FabLabValsamoggia/GustavoTheSpaceman/Mec/Modulo mp3/User Library-MP3-TF-16P.SLDASM

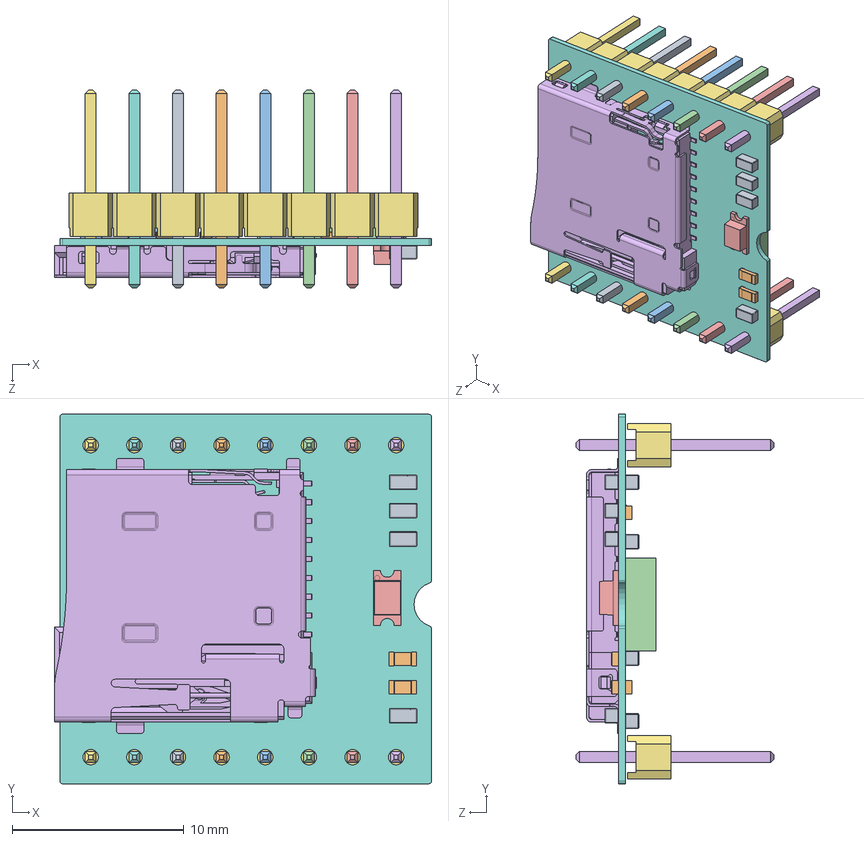
[picture p3: CAD file, 2020-09-24]
Mec/Modulo mp3/User Library-MP3-TF-16P.SLDASM
21.9 x 21.5 x 11.5 mm
User_Library-Chip_Capacitor2CAPC0603X33N x 13
User_Library-res0603-1 x 12
Extruded
Extruded_2
User_Library-FYLS-1206
User_Library-MEM2055-00-190-01-A_revG
Board
