FabLabValsamoggia/GustavoTheSpaceman/Mec/Componenti vari/capc/CAPC0603 v1.step

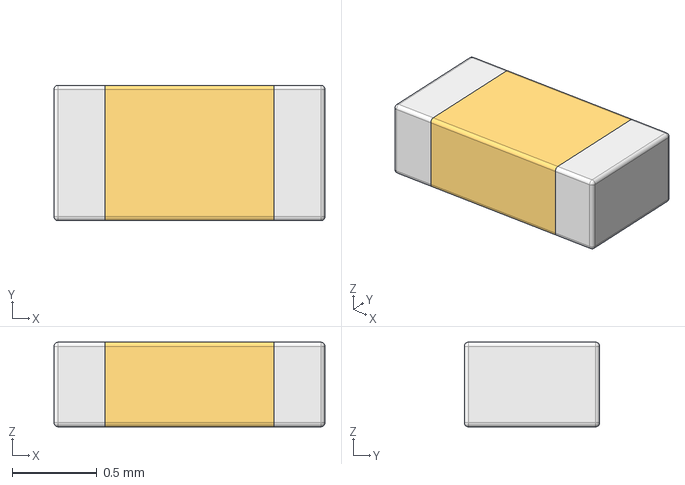
[picture p4: CAD file, 2020-09-24]
Mec/Componenti vari/capc/CAPC0603 v1.step
1.60 x 0.8 x 0.5 mm
