FabLabValsamoggia/GustavoTheSpaceman/Mec/Componenti vari/Push Button SMD/PZ_PushButton.stp

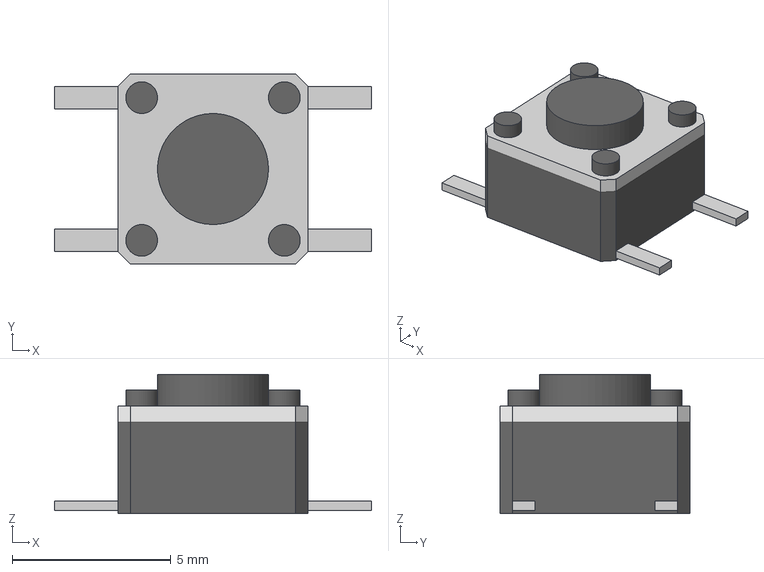
[picture p5: CAD file, 2020-09-24]
Mec/Componenti vari/Push Button SMD/PZ_PushButton.stp
10.0 x 6.00 x 4.40 mm
