FabLabValsamoggia/GustavoTheSpaceman/Mec/Componenti vari/strip/1x3 p2_54mm male.step

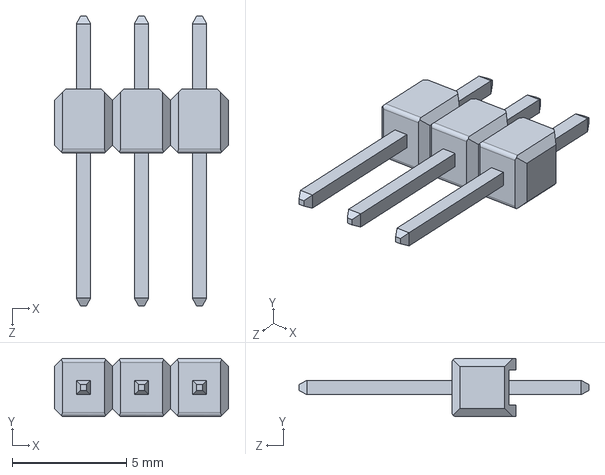
[picture p6: CAD file, 2020-09-24]
Mec/Componenti vari/strip/1x3 p2_54mm male.step
7.62 x 2.54 x 12.7 mm
