FabLabValsamoggia/GustavoTheSpaceman/Mec/Componenti vari/WS2812b/WS2812_RGB_LED_updated.stp

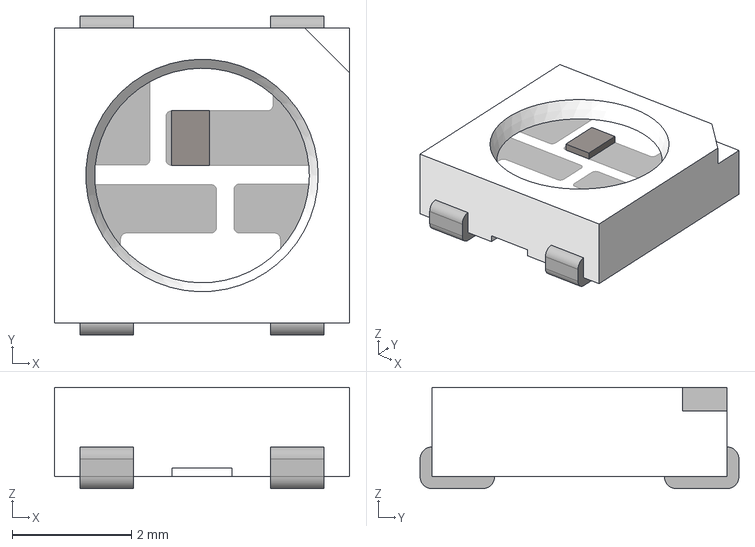
[picture p7: CAD file, 2020-09-24]
Mec/Componenti vari/WS2812b/WS2812_RGB_LED_updated.stp
4.95 x 5.35 x 1.70 mm
