FabLabValsamoggia/GustavoTheSpaceman/Mec/Gustavo/coperchio_rpv03.stl

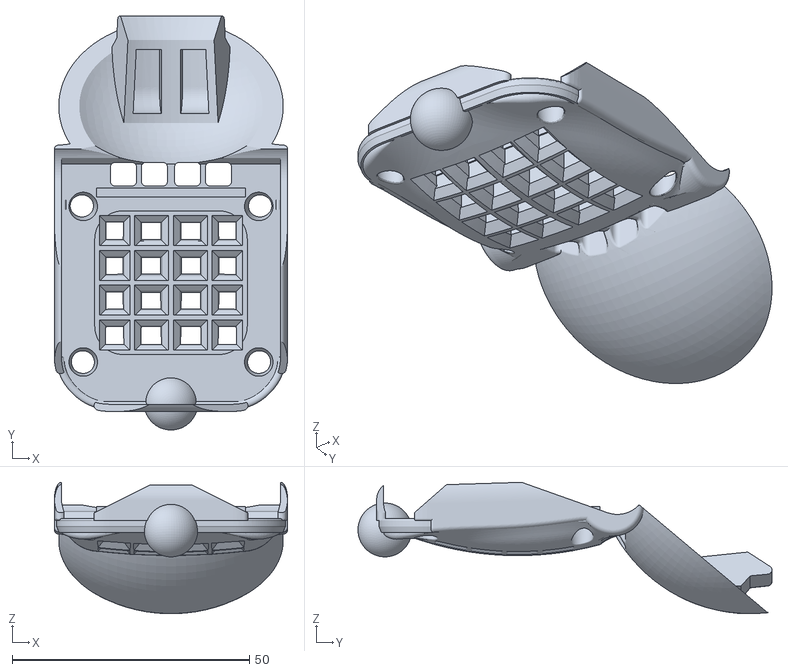
[picture p8: CAD file, 2020-09-24]
Mec/Gustavo/coperchio_rpv03.stl
49.2 x 87.3 x 27.7
