FabLabValsamoggia/GustavoTheSpaceman/Mec/Arduino Nano/Solidworks/User Library-Arduino Nano 3.0_User Library-SW3dPS-atmega8 (tqfp32)_V2008_.SLDPRT

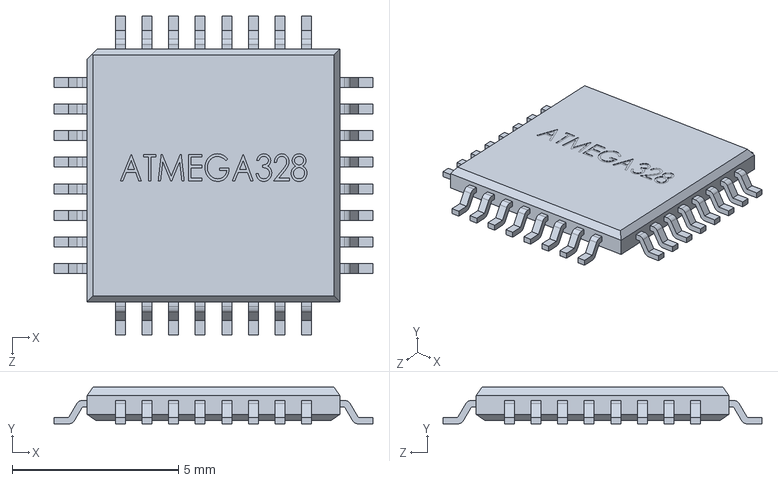
[picture p9: CAD file, 2020-09-24]
Mec/Arduino Nano/Solidworks/User Library-Arduino Nano 3.0_User Library-SW3dPS-atmega8 (tqfp32)_V2008_.SLDPRT
9.60 x 1.11 x 9.60 mm
