FabLabValsamoggia/GustavoTheSpaceman/Mec/Componenti vari/capc/CAPC1206 v2.step

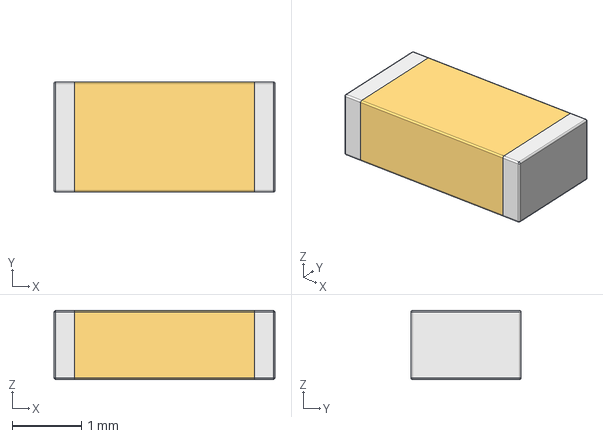
[picture p10: CAD file, 2020-09-24]
Mec/Componenti vari/capc/CAPC1206 v2.step
3.20 x 1.60 x 1.00 mm
