FabLabValsamoggia/GustavoTheSpaceman/Mec/Componenti vari/photoresistor.STEP

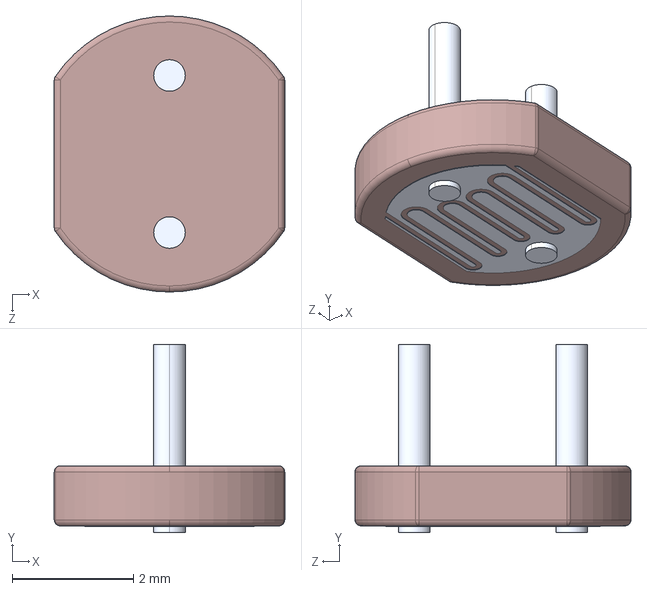
[picture p11: CAD file, 2020-09-24]
Mec/Componenti vari/photoresistor.STEP
3.80 x 3.10 x 4.55 mm
