FabLabValsamoggia/GustavoTheSpaceman/Mec/Componenti vari/strip/SSM-115-L-SV.stp

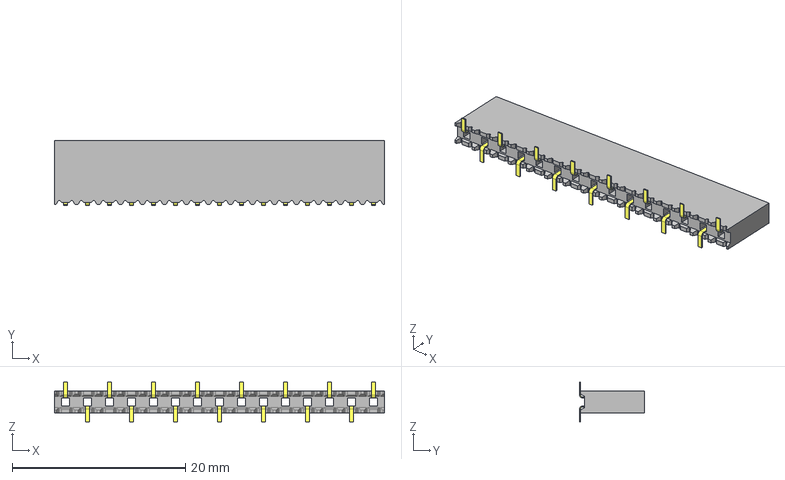
[picture p12: CAD file, 2020-09-24]
Mec/Componenti vari/strip/SSM-115-L-SV.stp
38.1 x 7.49 x 4.57 mm
_SSM-115-L-SV_body
_C-95-0215
