FabLabValsamoggia/GustavoTheSpaceman/Mec/Componenti vari/capc/CAPC0402 v2.step

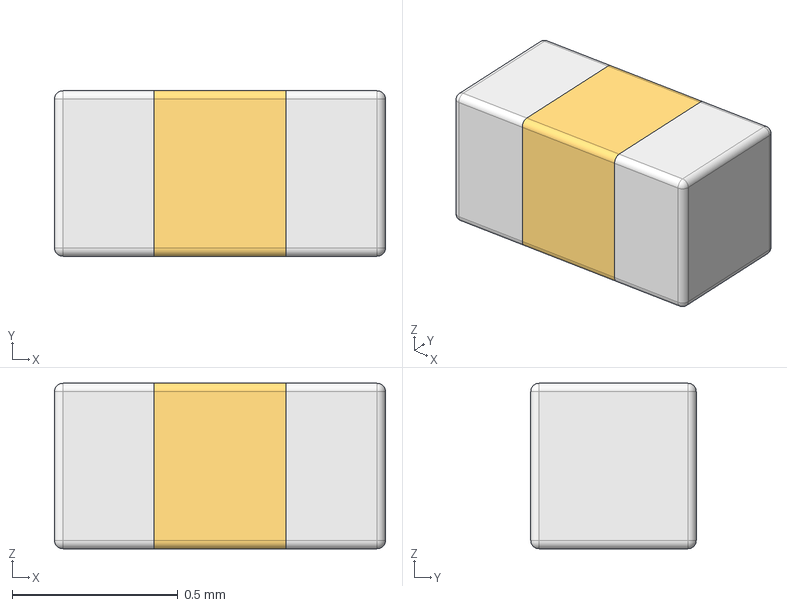
[picture p13: CAD file, 2020-09-24]
Mec/Componenti vari/capc/CAPC0402 v2.step
1.00 x 0.5 x 0.5 mm
