FabLabValsamoggia/GustavoTheSpaceman/Mec/Componenti vari/DO-214AA(SMB).STEP

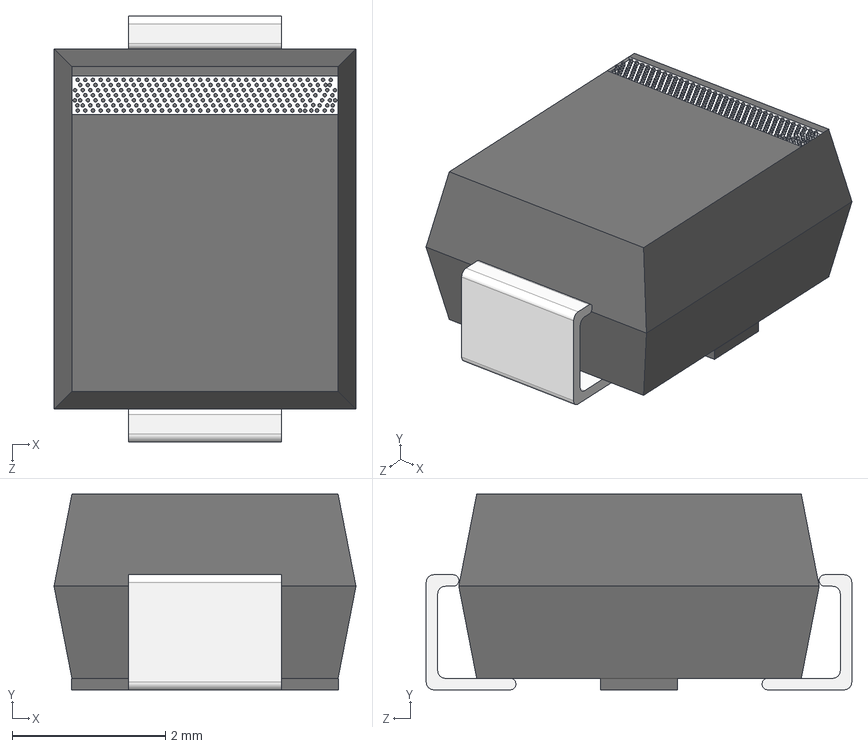
[picture p14: CAD file, 2020-09-24]
Mec/Componenti vari/DO-214AA(SMB).STEP
3.94 x 2.55 x 5.55 mm
