FabLabValsamoggia/GustavoTheSpaceman/Mec/Componenti vari/strip/1x2 p2.54mm male.step

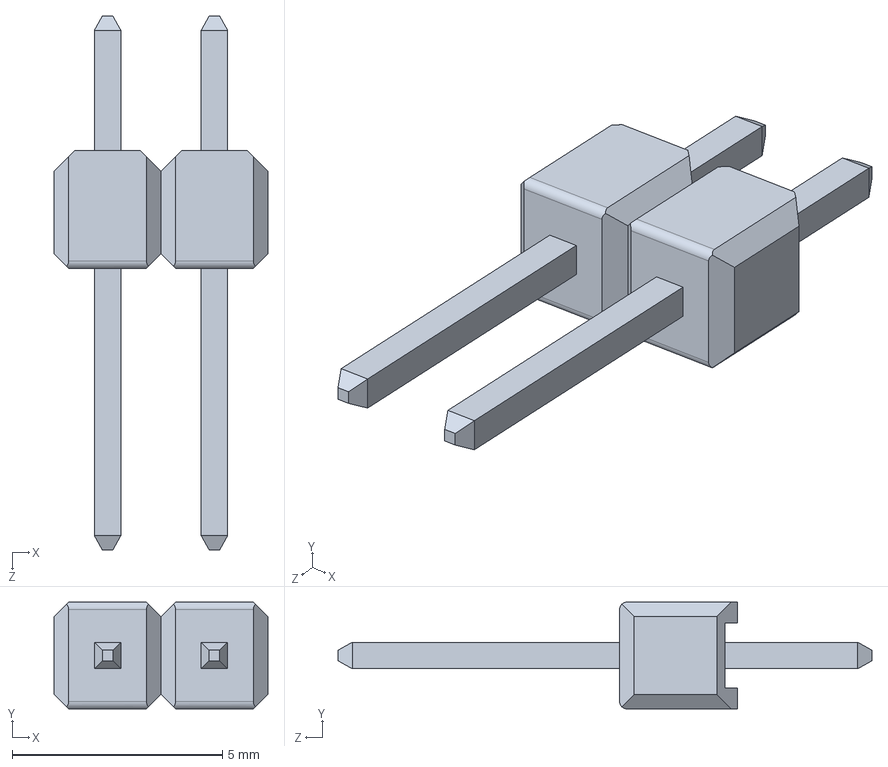
[picture p15: CAD file, 2020-09-24]
Mec/Componenti vari/strip/1x2 p2.54mm male.step
5.08 x 2.54 x 12.7 mm
