FabLabValsamoggia/GustavoTheSpaceman/Mec/Componenti vari/0805_RES.stp

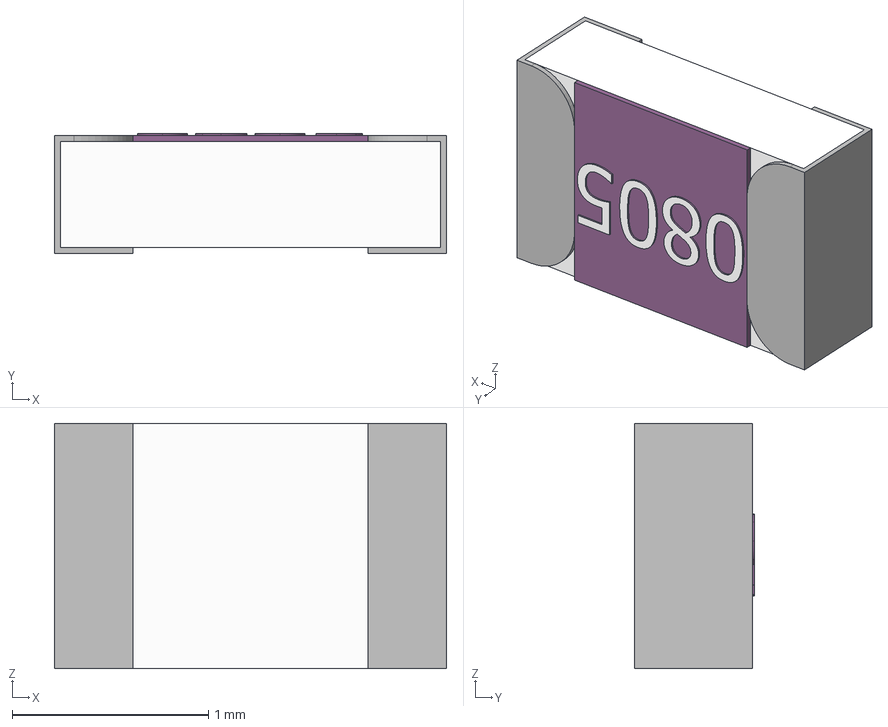
[picture p16: CAD file, 2020-09-24]
Mec/Componenti vari/0805_RES.stp
2.00 x 0.61 x 1.25 mm
Encapsulation x 2
capsule
TopCover
