FabLabValsamoggia/GustavoTheSpaceman/Mec/Componenti vari/capc/CAPC0805 v2.step

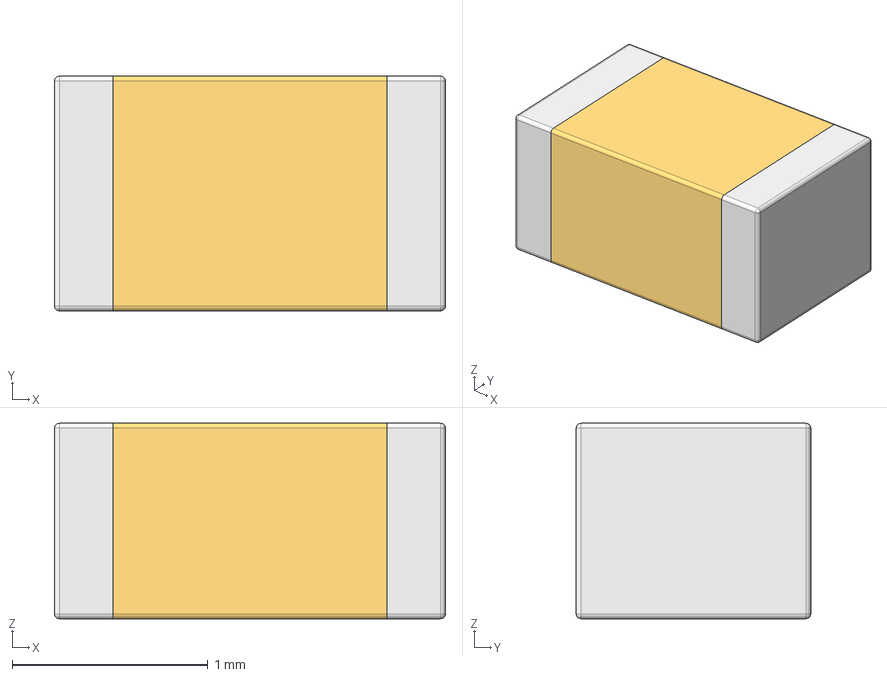
[picture p17: CAD file, 2020-09-24]
Mec/Componenti vari/capc/CAPC0805 v2.step
2.00 x 1.20 x 1.00 mm
