FabLabValsamoggia/GustavoTheSpaceman/Mec/Componenti vari/SSM-108-S-SV.stp

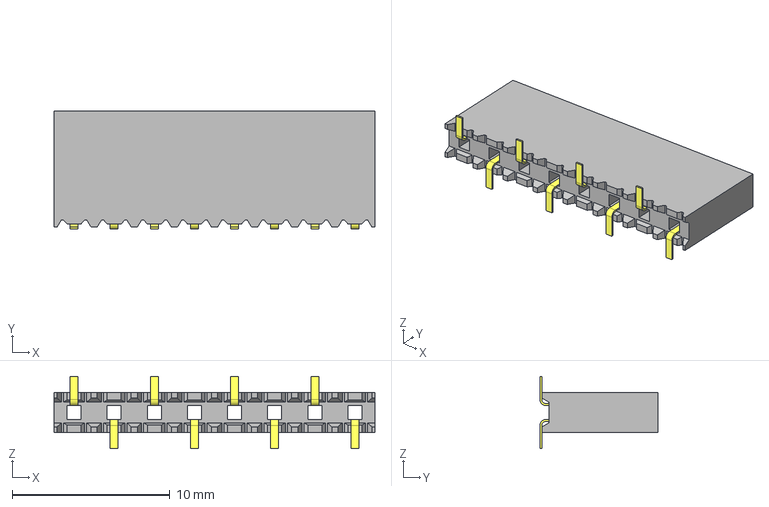
[picture p18: CAD file, 2020-09-24]
Mec/Componenti vari/SSM-108-S-SV.stp
20.3 x 7.49 x 4.57 mm
_SSM-108-S-SV_body
_C-95-028
