FabLabValsamoggia/GustavoTheSpaceman/Mec/Componenti vari/Diode SMA.stp

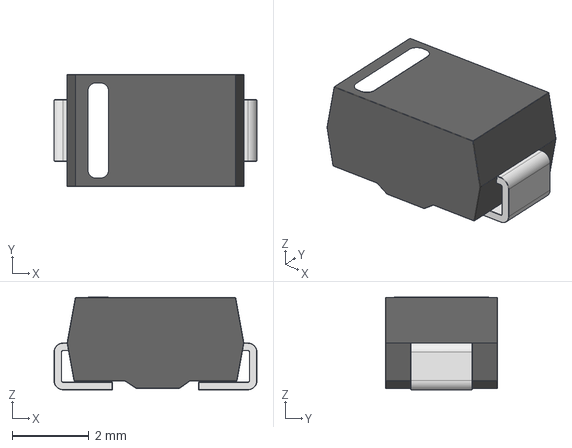
[picture p19: CAD file, 2020-09-24]
Mec/Componenti vari/Diode SMA.stp
5.28 x 2.92 x 2.41 mm
