FabLabValsamoggia/GustavoTheSpaceman/Mec/Componenti vari/TMX-12H.stp

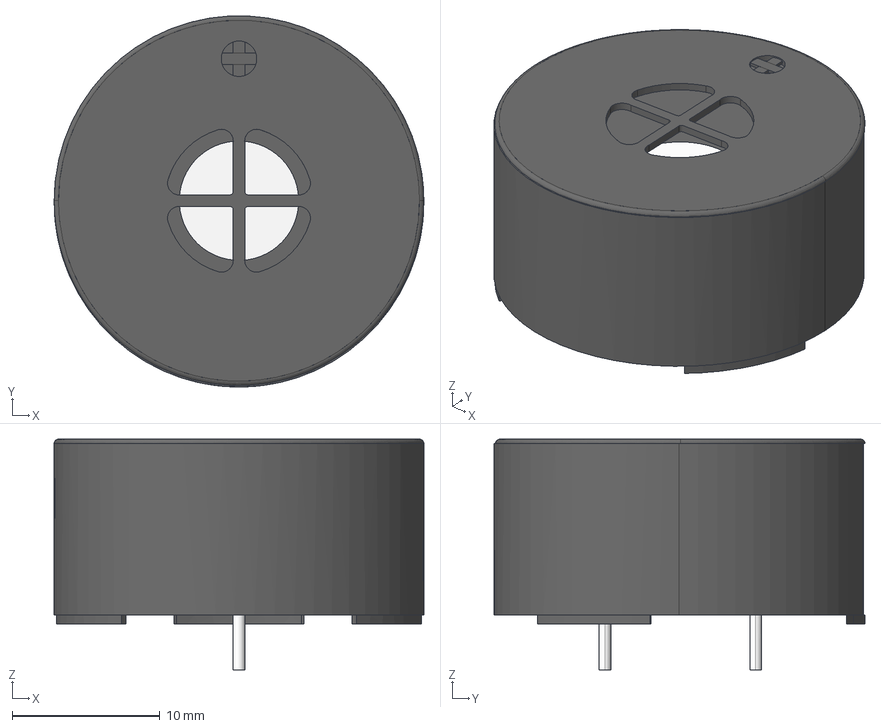
[picture p20: CAD file, 2020-09-24]
Mec/Componenti vari/TMX-12H.stp
25.0 x 25.1 x 15.6 mm
