FabLabValsamoggia/GustavoTheSpaceman/Mec/Arduino Nano/Solidworks/User Library-Arduino Nano 3.0_Arduino Nano 3.0 Bare PCB.SLDPRT

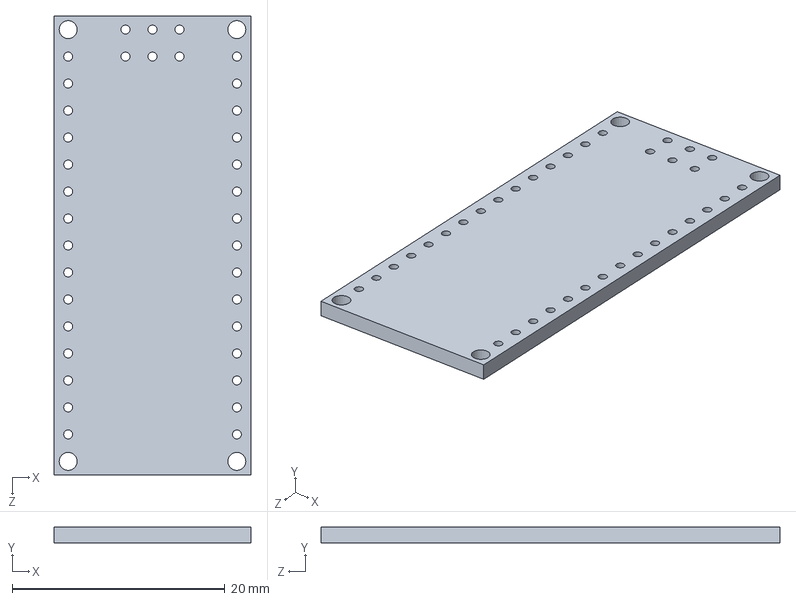
[picture p21: CAD file, 2020-09-24]
Mec/Arduino Nano/Solidworks/User Library-Arduino Nano 3.0_Arduino Nano 3.0 Bare PCB.SLDPRT
18.5 x 1.50 x 43.2 mm
