FabLabValsamoggia/GustavoTheSpaceman/Mec/Componenti vari/sot23 v2.step

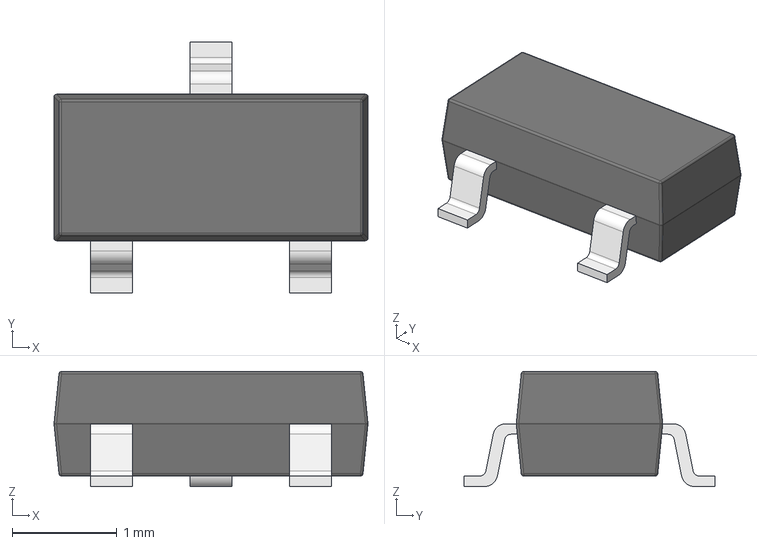
[picture p22: CAD file, 2020-09-24]
Mec/Componenti vari/sot23 v2.step
3.00 x 2.40 x 1.10 mm
pin x 3
