FabLabValsamoggia/GustavoTheSpaceman/Mec/Componenti vari/buzzer.stp

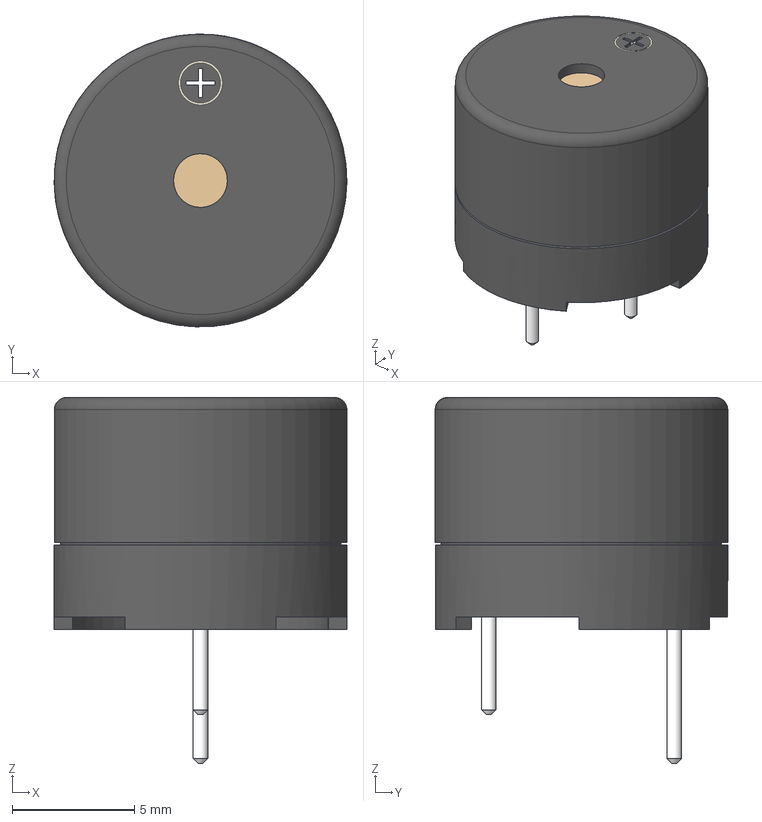
[picture p23: CAD file, 2020-09-24]
Mec/Componenti vari/buzzer.stp
12.0 x 12.0 x 15.0 mm
