FabLabValsamoggia/GustavoTheSpaceman/Mec/Componenti vari/Buzzer TDK.STEP

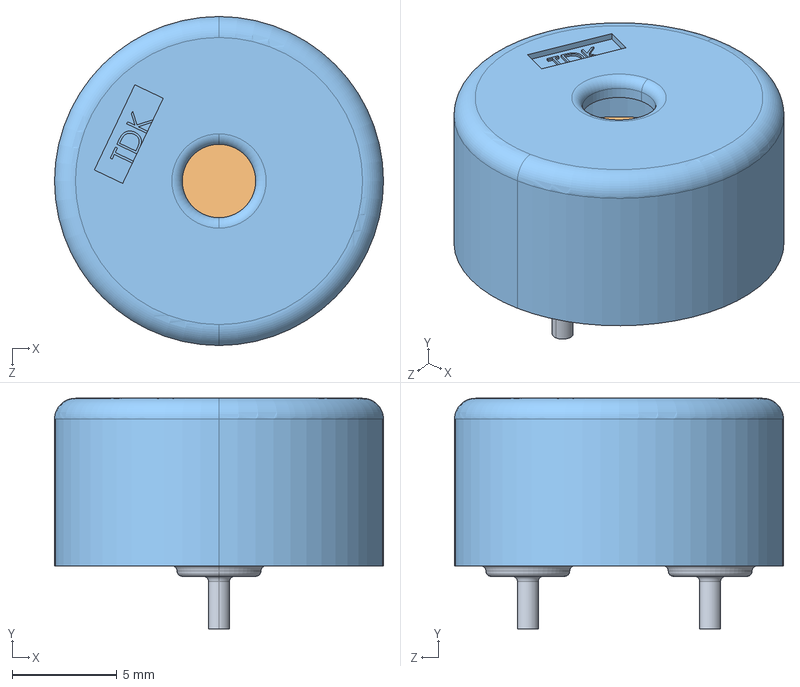
[picture p24: CAD file, 2020-09-24]
Mec/Componenti vari/Buzzer TDK.STEP
15.7 x 11.0 x 15.7 mm
