FabLabValsamoggia/GustavoTheSpaceman/Mec/Arduino Nano/Solidworks/User Library-Arduino Nano 3.0_Capacitor 0805.SLDPRT

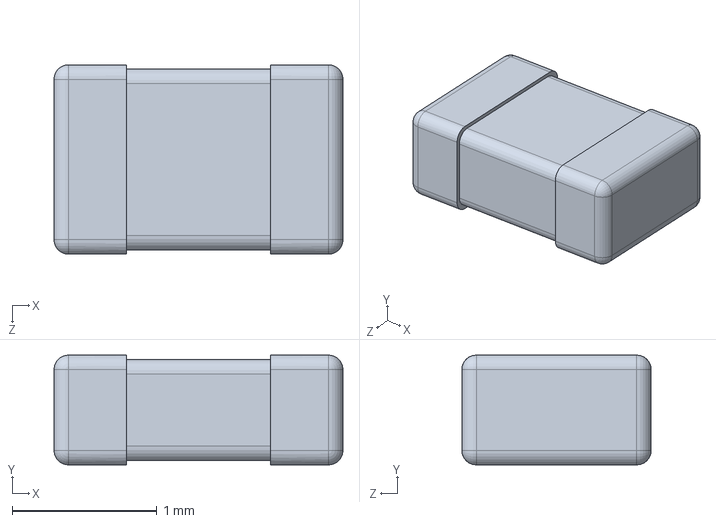
[picture p25: CAD file, 2020-09-24]
Mec/Arduino Nano/Solidworks/User Library-Arduino Nano 3.0_Capacitor 0805.SLDPRT
2.00 x 0.76 x 1.31 mm
