FabLabValsamoggia/GustavoTheSpaceman/Mec/Arduino Nano/Solidworks/User Library-Arduino Nano 3.0_User Library-SSOP-28-FT232RL_.SLDPRT

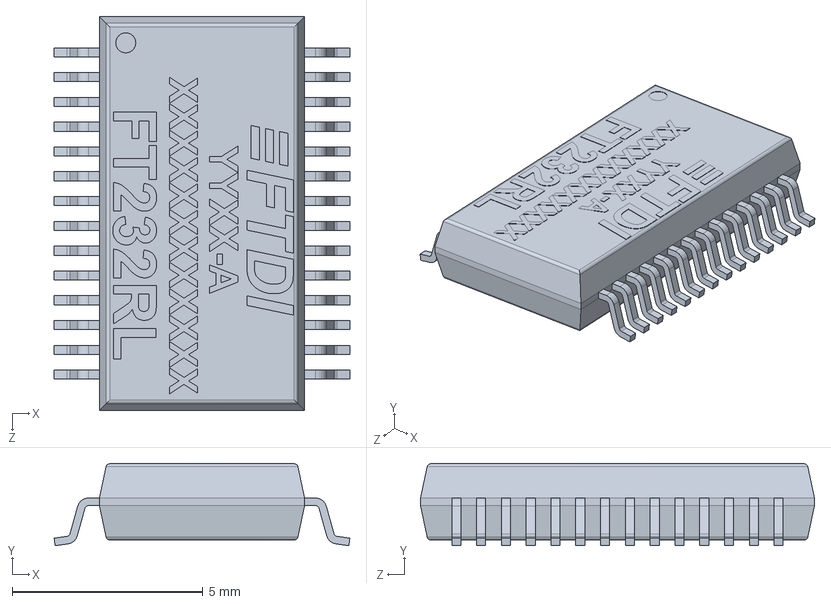
[picture p26: CAD file, 2020-09-24]
Mec/Arduino Nano/Solidworks/User Library-Arduino Nano 3.0_User Library-SSOP-28-FT232RL_.SLDPRT
7.76 x 2.16 x 10.3 mm
