FabLabValsamoggia/GustavoTheSpaceman/Mec/Arduino Nano/Solidworks/User Library-Arduino Nano 3.0_LED 1206 Blue.SLDPRT

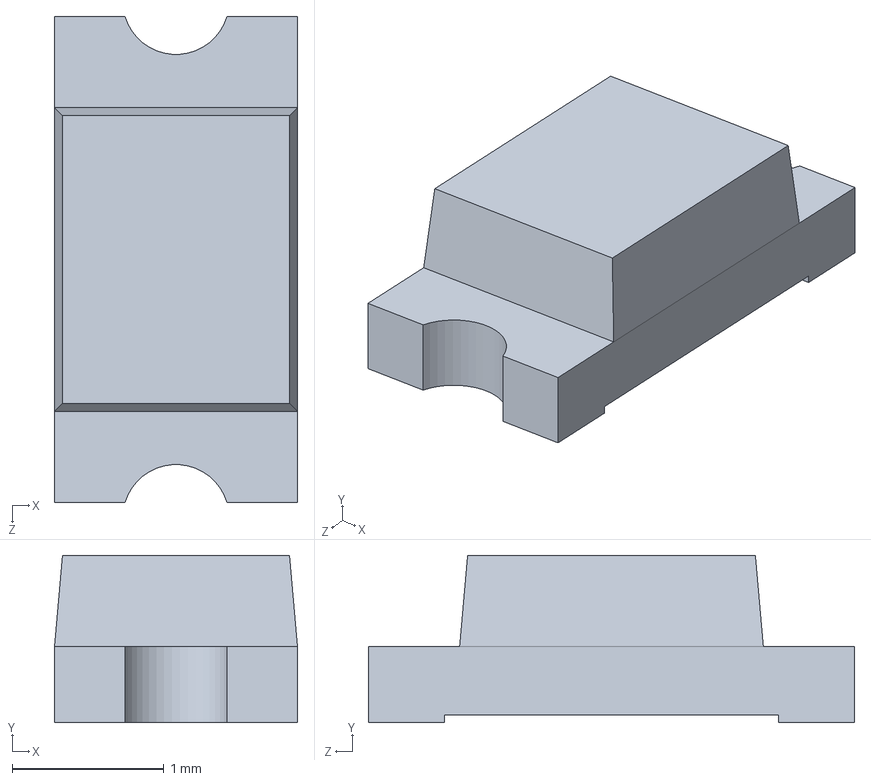
[picture p27: CAD file, 2020-09-24]
Mec/Arduino Nano/Solidworks/User Library-Arduino Nano 3.0_LED 1206 Blue.SLDPRT
1.60 x 1.10 x 3.20 mm
