FabLabValsamoggia/GustavoTheSpaceman/Mec/Arduino Nano/Solidworks/User Library-Arduino Nano 3.0_HDR2x3.SLDPRT

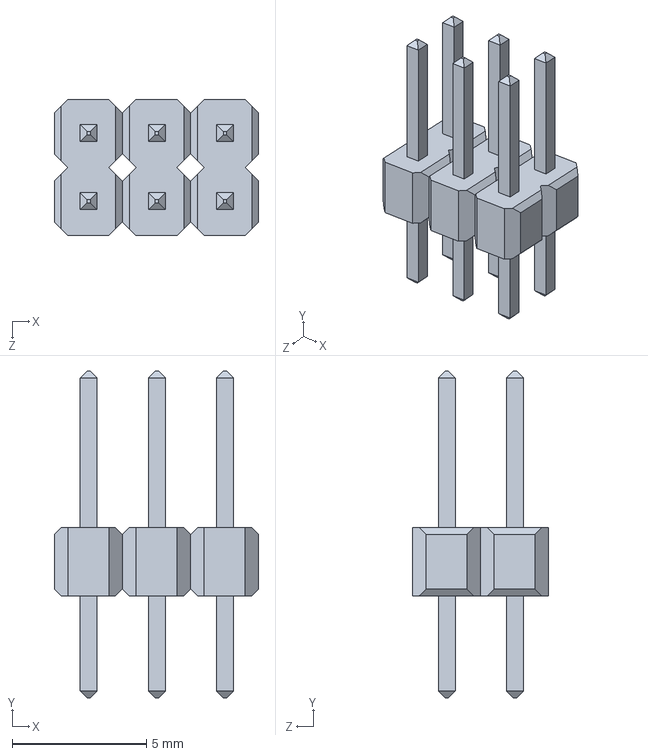
[picture p28: CAD file, 2020-09-24]
Mec/Arduino Nano/Solidworks/User Library-Arduino Nano 3.0_HDR2x3.SLDPRT
7.62 x 12.2 x 5.08 mm
