FabLabValsamoggia/GustavoTheSpaceman/Mec/Arduino Nano/Solidworks/User Library-Arduino Nano 3.0_SOT-223.SLDPRT

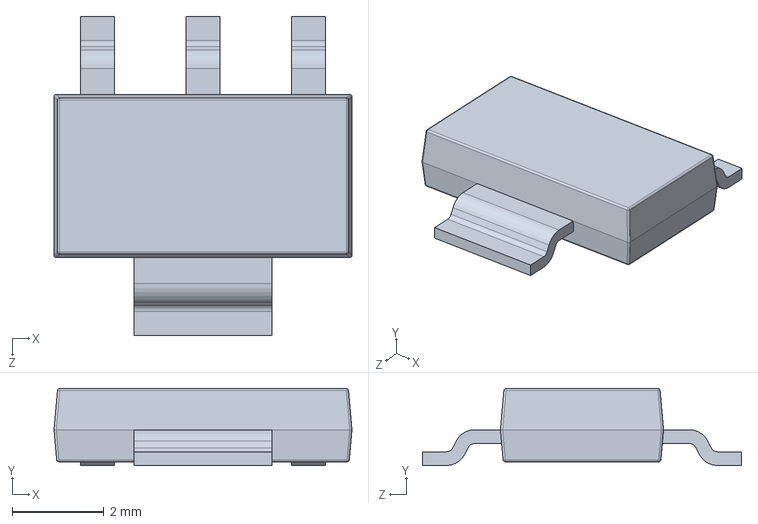
[picture p29: CAD file, 2020-09-24]
Mec/Arduino Nano/Solidworks/User Library-Arduino Nano 3.0_SOT-223.SLDPRT
6.50 x 1.68 x 6.96 mm
