FabLabValsamoggia/GustavoTheSpaceman/Mec/Arduino Nano/Solidworks/User Library-Arduino Nano 3.0_HDR1x15.SLDPRT

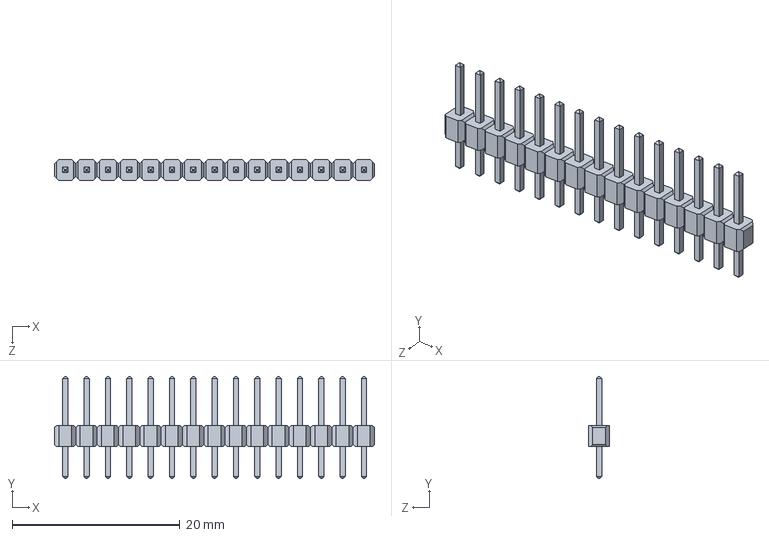
[picture p30: CAD file, 2020-09-24]
Mec/Arduino Nano/Solidworks/User Library-Arduino Nano 3.0_HDR1x15.SLDPRT
38.1 x 12.2 x 2.54 mm
