FabLabValsamoggia/GustavoTheSpaceman/Mec/Arduino Nano/Solidworks/User Library-Arduino Nano 3.0_User Library-Tantalum Capacitor Case R_Tantalum case R part1.SLDPRT

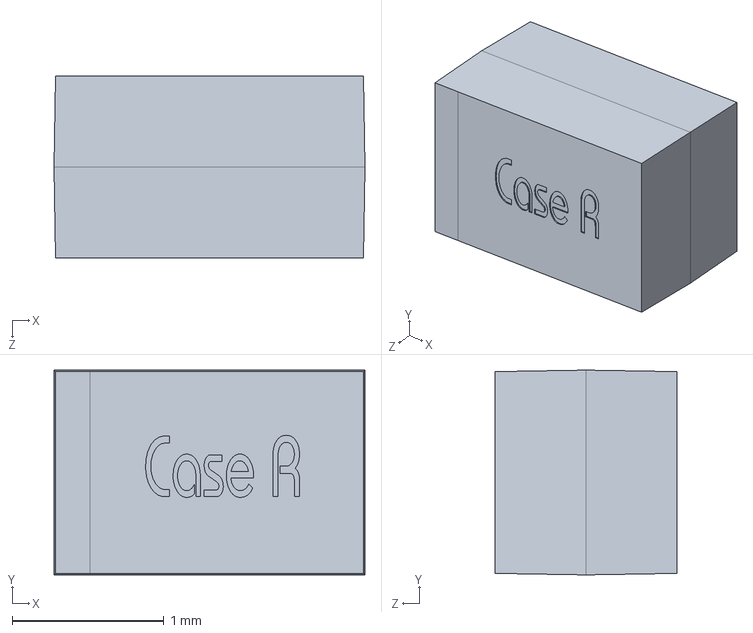
[picture p31: CAD file, 2020-09-24]
Mec/Arduino Nano/Solidworks/User Library-Arduino Nano 3.0_User Library-Tantalum Capacitor Case R_Tantalum case R part1.SLDPRT
2.05 x 1.35 x 1.20 mm
