FabLabValsamoggia/GustavoTheSpaceman/Mec/Arduino Nano/Solidworks/User Library-Arduino Nano 3.0_User Library-Tantalum Capacitor Case R_Tantalum case R part2.SLDPRT

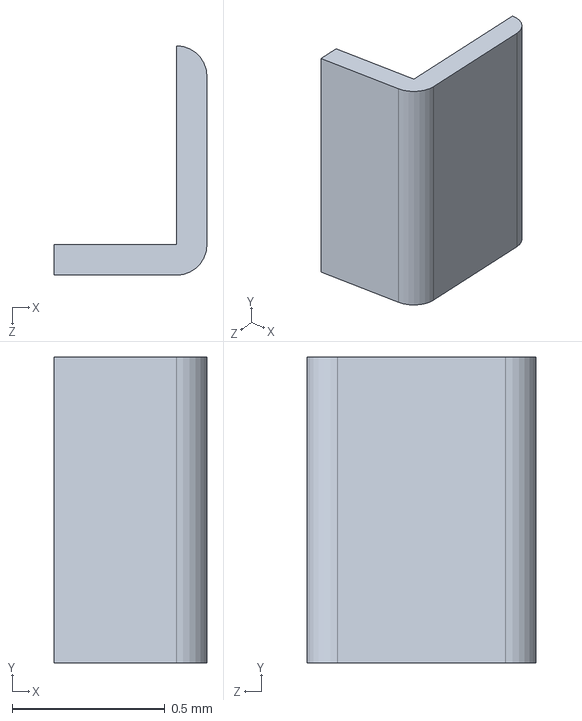
[picture p32: CAD file, 2020-09-24]
Mec/Arduino Nano/Solidworks/User Library-Arduino Nano 3.0_User Library-Tantalum Capacitor Case R_Tantalum case R part2.SLDPRT
0.5 x 1.00 x 0.75 mm
