FabLabValsamoggia/GustavoTheSpaceman/Mec/Arduino Nano/Solidworks/User Library-Arduino Nano 3.0_User Library-548190572_USBBMINI_.SLDPRT

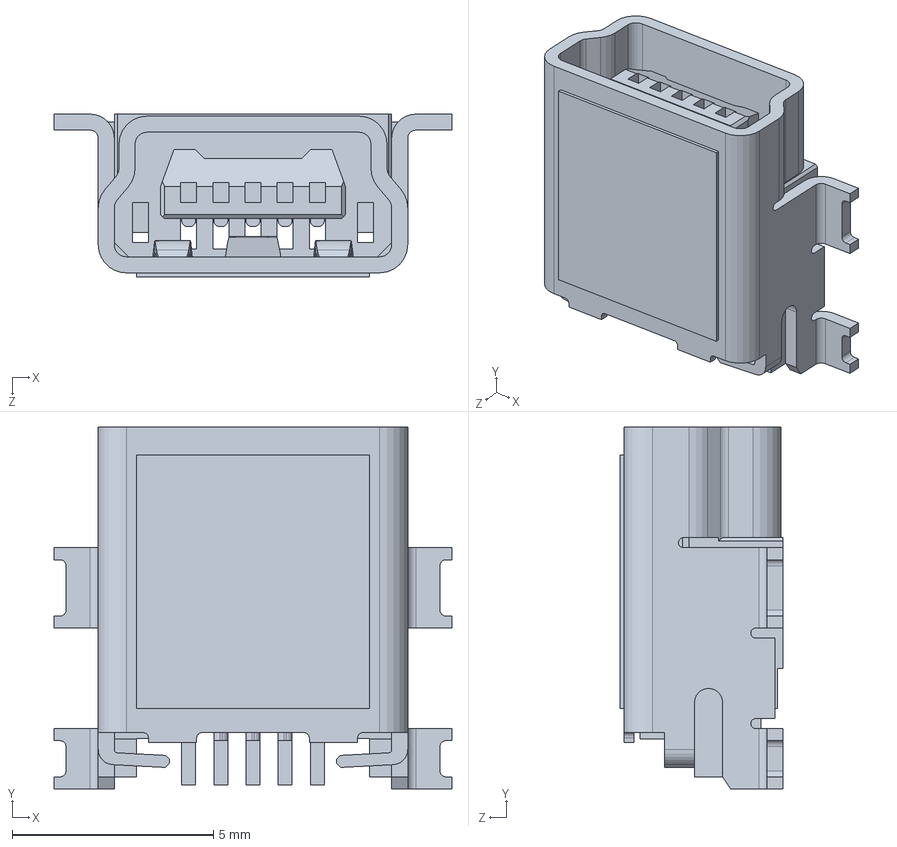
[picture p33: CAD file, 2020-09-24]
Mec/Arduino Nano/Solidworks/User Library-Arduino Nano 3.0_User Library-548190572_USBBMINI_.SLDPRT
9.90 x 9.00 x 4.05 mm
