FabLabValsamoggia/GustavoTheSpaceman/Mec/Arduino Nano/Solidworks/User Library-Arduino Nano 3.0_User Library-TUMD2.sldasm

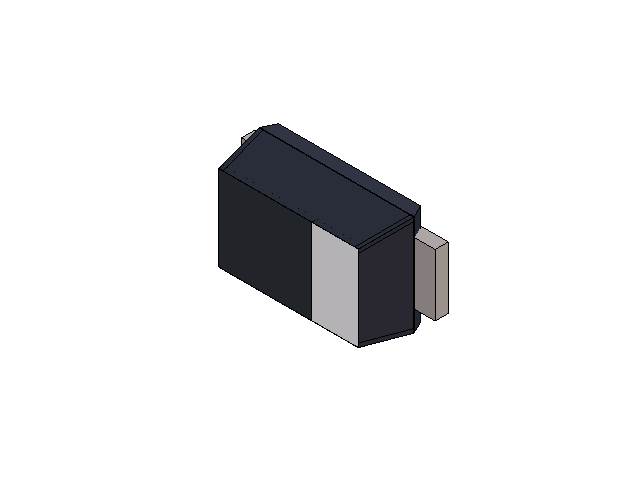
[picture p35: CAD file, 2020-09-24]
Mec/Arduino Nano/Solidworks/User Library-Arduino Nano 3.0_User Library-TUMD2.sldasm
User Library-Arduino Nano 3.0_User Library-TUMD2_Extruded x 2
User Library-Arduino Nano 3.0_User Library-TUMD2_Extruded_2 x 2
User Library-Arduino Nano 3.0_User Library-TUMD2_Extruded_3
User Library-Arduino Nano 3.0_User Library-TUMD2_Extruded_4
User Library-Arduino Nano 3.0_User Library-TUMD2_Extruded_5
User Library-Arduino Nano 3.0_User Library-TUMD2_Extruded_6
User Library-Arduino Nano 3.0_User Library-TUMD2_Extruded_7
