FabLabValsamoggia/GustavoTheSpaceman/Mec/Arduino Nano/Solidworks/User Library-Arduino Nano 3.0_User Library-CSTCE_V-1.sldasm

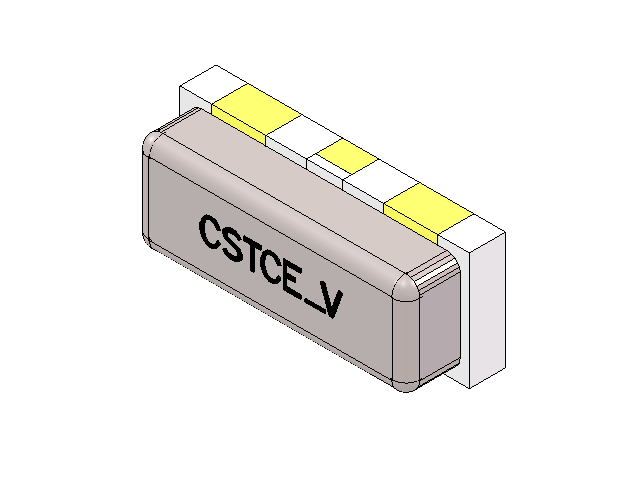
[picture p36: CAD file, 2020-09-24]
Mec/Arduino Nano/Solidworks/User Library-Arduino Nano 3.0_User Library-CSTCE_V-1.sldasm
User Library-Arduino Nano 3.0_User Library-CSTCE_V-1_Board1
User Library-Arduino Nano 3.0_User Library-CSTCE_V-1_Extruded20
User Library-Arduino Nano 3.0_User Library-CSTCE_V-1_Extruded15
User Library-Arduino Nano 3.0_User Library-CSTCE_V-1_Extruded14 x 2
User Library-Arduino Nano 3.0_User Library-CSTCE_V-1_Extruded17
User Library-Arduino Nano 3.0_User Library-CSTCE_V-1_Extruded21
User Library-Arduino Nano 3.0_User Library-CSTCE_V-1_Extruded25
User Library-Arduino Nano 3.0_User Library-CSTCE_V-1_Extruded23
User Library-Arduino Nano 3.0_User Library-CSTCE_V-1_Extruded18 x 2
User Library-Arduino Nano 3.0_User Library-CSTCE_V-1_Extruded16
User Library-Arduino Nano 3.0_User Library-CSTCE_V-1_Extruded13
User Library-Arduino Nano 3.0_User Library-CSTCE_V-1_Extruded24 x 2
User Library-Arduino Nano 3.0_User Library-CSTCE_V-1_Extruded22 x 2
User Library-Arduino Nano 3.0_User Library-CSTCE_V-1_Sphere1 x 4
User Library-Arduino Nano 3.0_User Library-CSTCE_V-1_Cylinder3 x 2
User Library-Arduino Nano 3.0_User Library-CSTCE_V-1_Cylinder2 x 2
User Library-Arduino Nano 3.0_User Library-CSTCE_V-1_Extruded19
