FabLabValsamoggia/GustavoTheSpaceman/Mec/Arduino Nano/Solidworks/User Library-Arduino Nano 3.0_User Library-Array-1206-4Way-Var2-1.sldasm

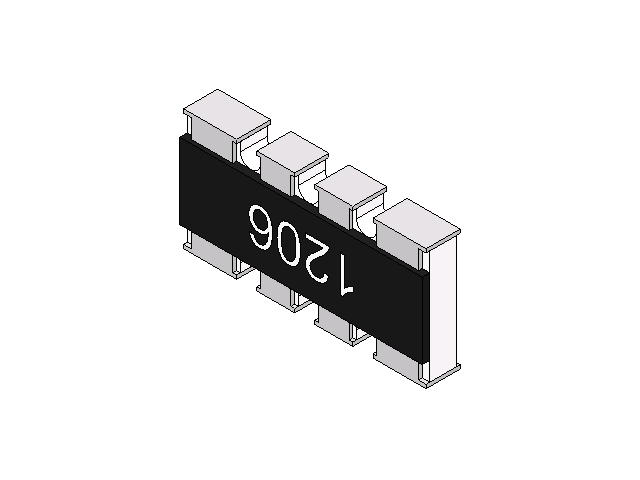
[picture p37: CAD file, 2020-09-24]
Mec/Arduino Nano/Solidworks/User Library-Arduino Nano 3.0_User Library-Array-1206-4Way-Var2-1.sldasm
User Library-Arduino Nano 3.0_User Library-Array-1206-4Way-Var2-1_Anschl_X_FCsse_1
User Library-Arduino Nano 3.0_User Library-Array-1206-4Way-Var2-1_K_X_F6rper_1
User Library-Arduino Nano 3.0_User Library-Array-1206-4Way-Var2-1_Deckel_1
User Library-Arduino Nano 3.0_User Library-Array-1206-4Way-Var2-1_Beschriftung_1
