FabLabValsamoggia/GustavoTheSpaceman/Docs/TestButton.png

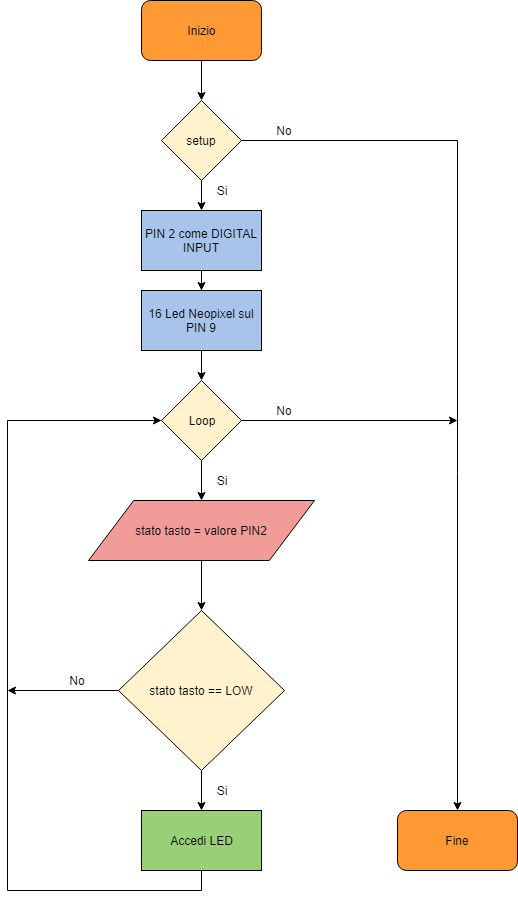
Docs/TestButton.png
